ieb/SolaryVoltageSwitch/pcb/mosfet.asc

D1: LED; NSCW100
M1: nmos; IRL530NS_L
Q1: npn; BC817-25
R1: res; 10
R2: res; 10K
R3: res; 1K
R4: res; 1K
R5: res; 0.001R
U1: PC817A
V1: voltage; PULSE(0 5 0.1 0.001 0.001 0.1 0.3 10)
V2: voltage; 12
Named nets: 0
.tran 1s startup
